B-S200502/Capstone_490_Software/hardware/3D_Design/component_step_files/pi_camera_g_detailed.step

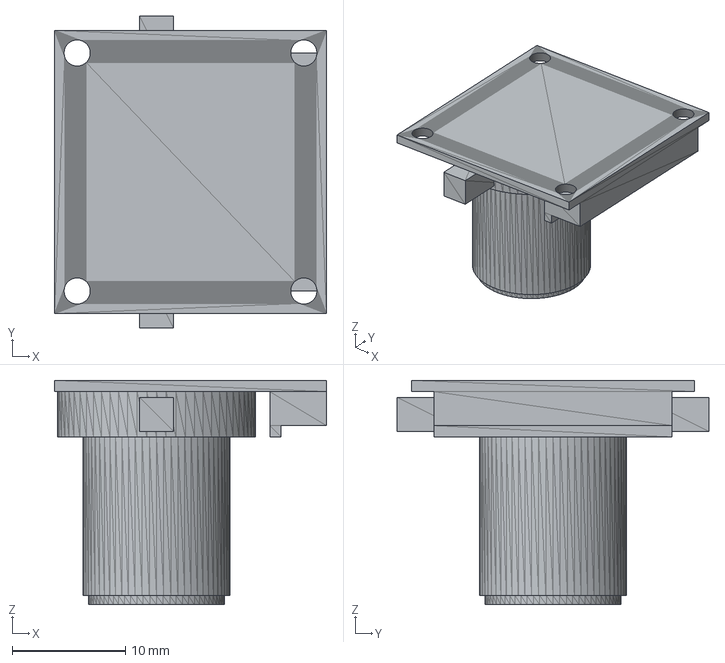
[picture p15: CAD file, 2026-03-08]
hardware/3D_Design/component_step_files/pi_camera_g_detailed.step
24.0 x 27.5 x 19.8 mm
