B-S200502/Capstone_490_Software/hardware/3D_Design/just_in_case_saves/V2_AC_test1.FCStd

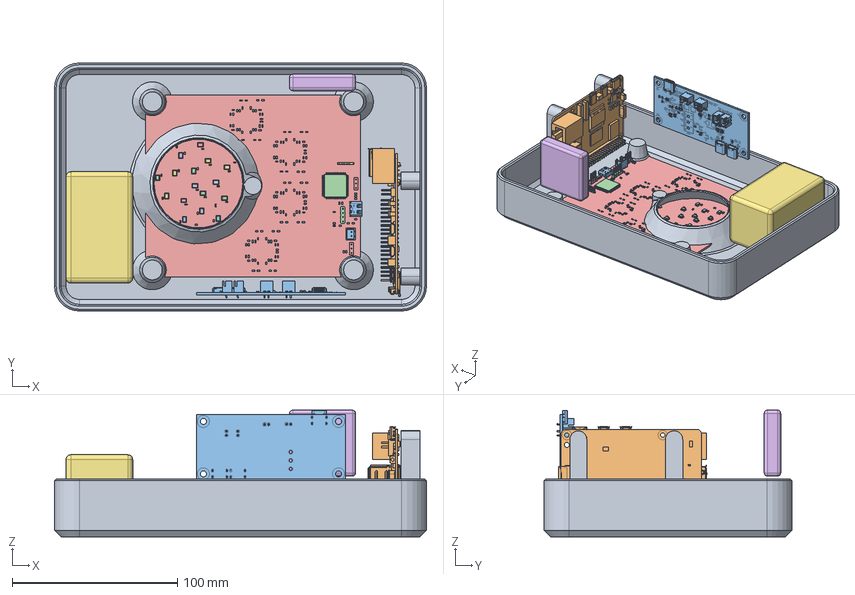
[picture p16: CAD file, 2026-03-08]
hardware/3D_Design/just_in_case_saves/V2_AC_test1.FCStd
225.0 x 150.0 x 76.7 mm
Back
Pi5
PowerBoard
R_0603_1608Metric
C_0603_1608Metric
R_0603_1608Metric001
MIC-SMD_6P_L3.5-W2.7_SPH1878LR5H-1
R_0603_1608Metric002
R_0603_1608Metric003
C_0603_1608Metric001
R_0603_1608Metric004
R_0603_1608Metric005
R_0603_1608Metric006
C_0603_1608Metric002
R_0603_1608Metric007
R_0603_1608Metric008
R_0603_1608Metric009
R_0603_1608Metric010
MIC-SMD_6P_L3.5-W2.7_SPH1878LR5H-002
R_0603_1608Metric011
PinHeader_1x03_P2.54mm_Vertical
R_0603_1608Metric012
R_0603_1608Metric013
R_0603_1608Metric014
R_0603_1608Metric015
R_0603_1608Metric016
R_0603_1608Metric017
MIC-SMD_6P_L3.5-W2.7_SPH1878LR5H-003
R_0603_1608Metric018
R_0603_1608Metric019
R_0603_1608Metric020
C_0603_1608Metric003
R_0603_1608Metric021
R_0603_1608Metric022
R_0603_1608Metric023
C_0603_1608Metric004
R_0603_1608Metric024
R_0603_1608Metric025
MIC-SMD_6P_L3.5-W2.7_SPH1878LR5H-004
R_0603_1608Metric026
R_0603_1608Metric027
C_0603_1608Metric005
R_0603_1608Metric028
R_0603_1608Metric029
R_0603_1608Metric030
R_0603_1608Metric031
R_0603_1608Metric032
R_0603_1608Metric033
C_0603_1608Metric006
R_0603_1608Metric034
C_0603_1608Metric007
R_0603_1608Metric035
R_0603_1608Metric036
R_0603_1608Metric037
R_0603_1608Metric038
R_0603_1608Metric039
R_0603_1608Metric040
R_0603_1608Metric041
R_0603_1608Metric042
R_0603_1608Metric043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
