B-S200502/Capstone_490_Software/hardware/3D_Design/result_step_files/BACK-AcousticImager-Fusion001.step

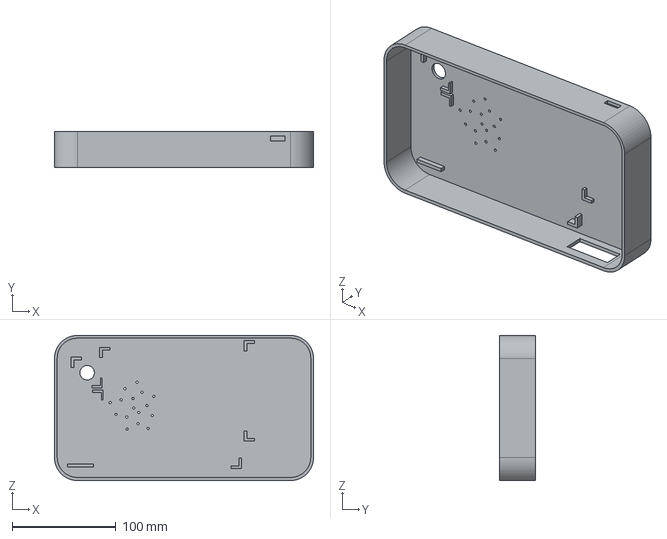
[picture p17: CAD file, 2026-02-12]
hardware/3D_Design/result_step_files/BACK-AcousticImager-Fusion001.step
250.0 x 35.0 x 140.0 mm
