B-S200502/Capstone_490_Software/src/hardware/result_step_files/bottom/BL_sink.step

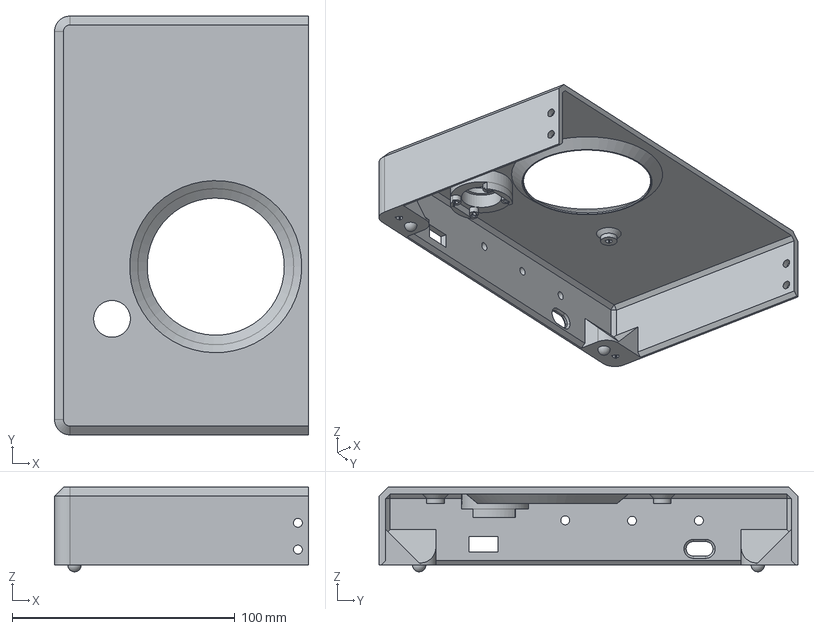
[picture p18: CAD file, 2026-05-04]
src/hardware/result_step_files/bottom/BL_sink.step
114.0 x 188.0 x 38.0 mm
