B-S200502/Capstone_490_Software/src/hardware/result_step_files/top/TL.step

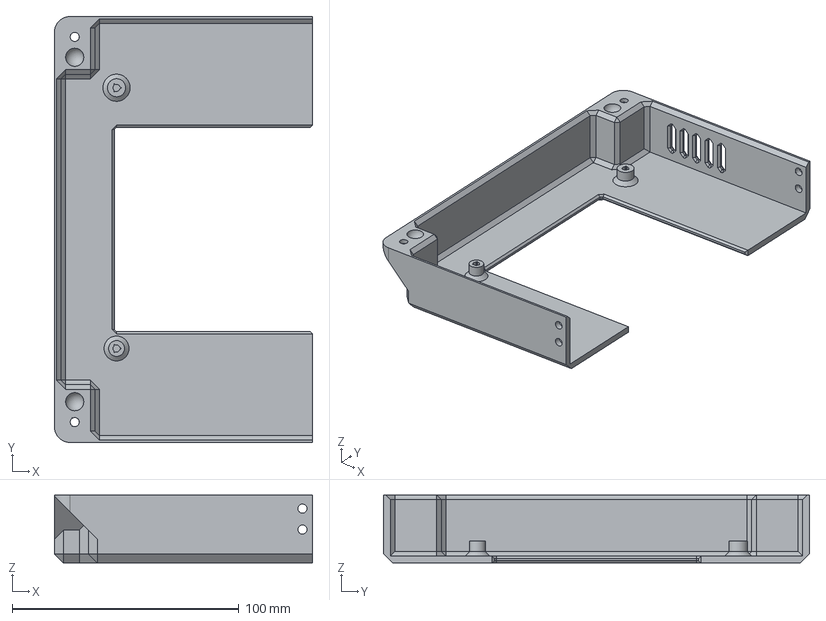
[picture p19: CAD file, 2026-05-04]
src/hardware/result_step_files/top/TL.step
114.0 x 188.0 x 30.0 mm
