B-S200502/Capstone_490_Software/hardware/3D_Design/component_step_files/low_level_components/SPH8878LR5H_1_Accurate.step

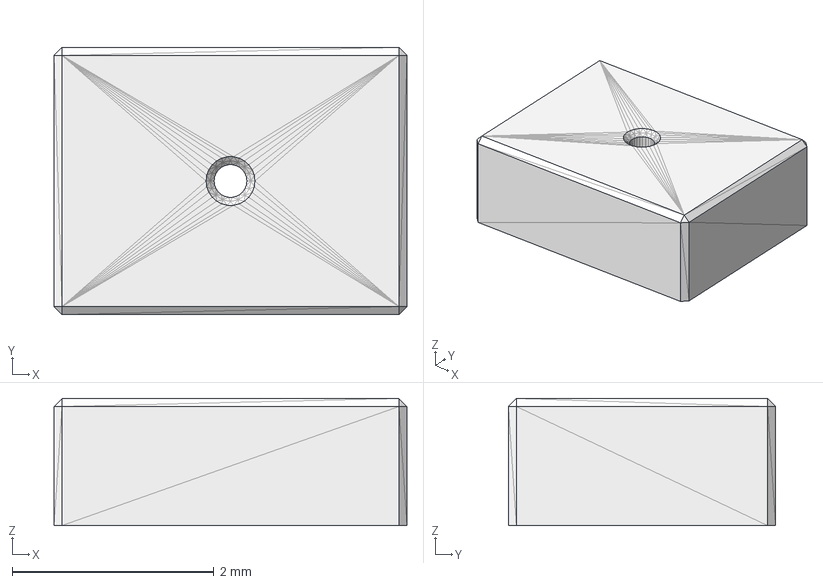
[picture p20: CAD file, 2026-02-10]
hardware/3D_Design/component_step_files/low_level_components/SPH8878LR5H_1_Accurate.step
3.50 x 2.65 x 1.26 mm
