B-S200502/Capstone_490_Software/hardware/3D_Design/component_step_files/Power Board.step

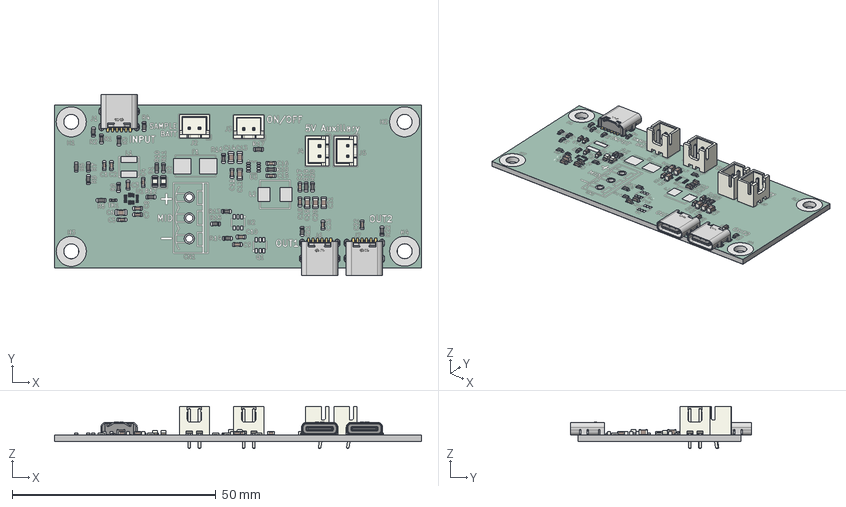
[picture p21: CAD file, 2026-02-10]
hardware/3D_Design/component_step_files/Power Board.step
90.0 x 44.4 x 10.4 mm
C_0805_2012Metric x 7
R_0603_1608Metric x 22
USB-C-SMD_TYPE-C-6P-WTL8.35-108 x 3
LED_0805_2012Metric x 2
JST_XH_B2B-XH-A_1x02_P2.50mm_Vertical x 4
C_0603_1608Metric x 16
R_0402_1005Metric
Power Board_copper
Power Board_pad
Power Board_via
Power Board_silkscreen
Power Board_soldermask x 2
Power Board_PCB
