B-S200502/Capstone_490_Software/hardware/3D_Design/just_in_case_saves/AcousticImager.FCStd

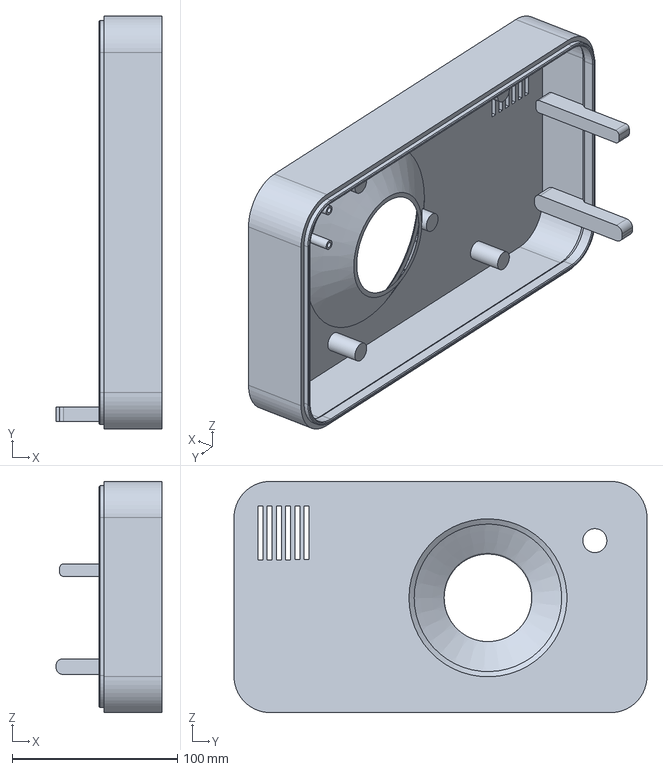
[picture p22: CAD file, 2026-03-08]
hardware/3D_Design/just_in_case_saves/AcousticImager.FCStd
64.0 x 250.0 x 140.0 mm
