B-S200502/Capstone_490_Software/hardware/3D_Design/component_step_files/lcd 7inch cap 1024 600.step

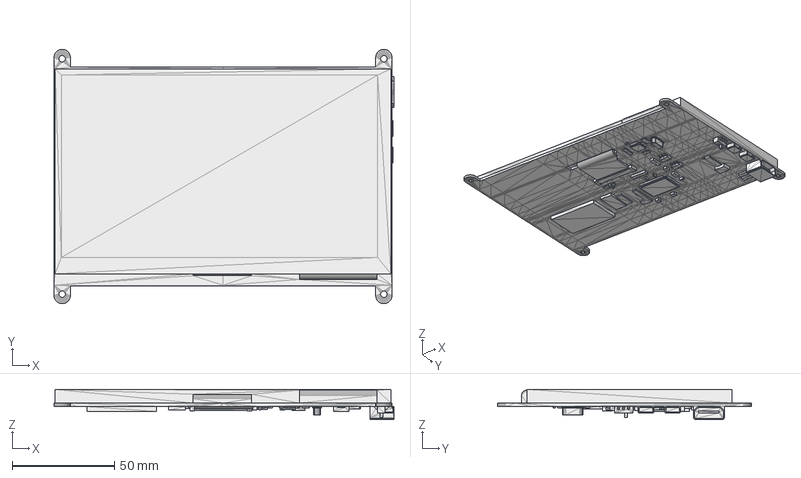
[picture p23: CAD file, 2026-02-10]
hardware/3D_Design/component_step_files/lcd 7inch cap 1024 600.step
166.0 x 124.3 x 14.8 mm
