B-S200502/Capstone_490_Software/hardware/3D_Design/component_step_files/low_level_components/QFP50P2200X2200X160-144N.step

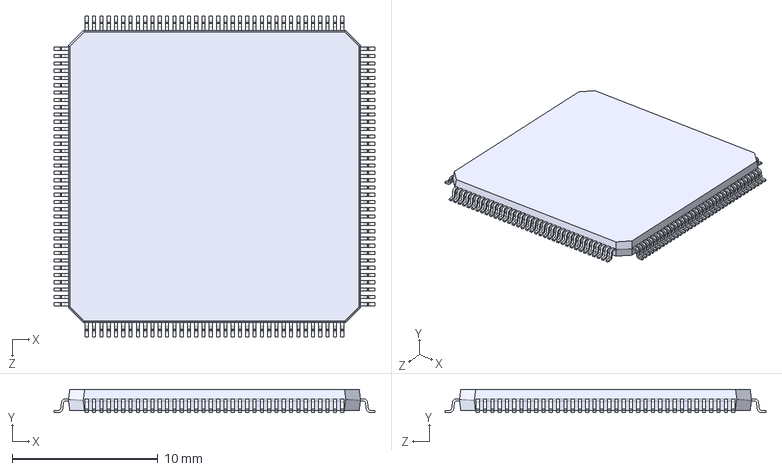
[picture p24: CAD file, 2026-02-10]
hardware/3D_Design/component_step_files/low_level_components/QFP50P2200X2200X160-144N.step
22.0 x 1.60 x 22.0 mm
