B-S200502/Capstone_490_Software/hardware/3D_Design/component_step_files/low_level_components/TPH2504-TR.stp

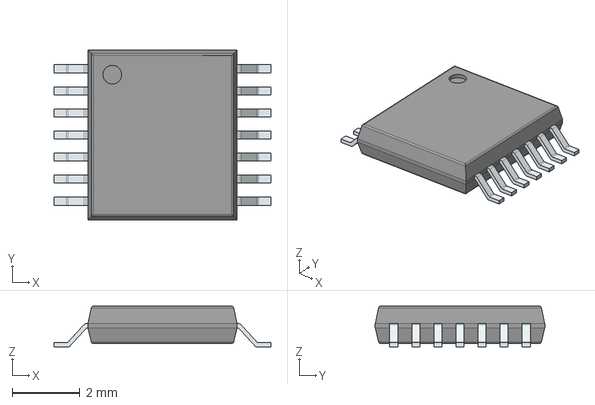
[picture p25: CAD file, 2026-02-10]
hardware/3D_Design/component_step_files/low_level_components/TPH2504-TR.stp
6.40 x 5.00 x 1.20 mm
PinsArrayLR
