B-S200502/Capstone_490_Software/hardware/3D_Design/component_step_files/RaspberryPi5.step

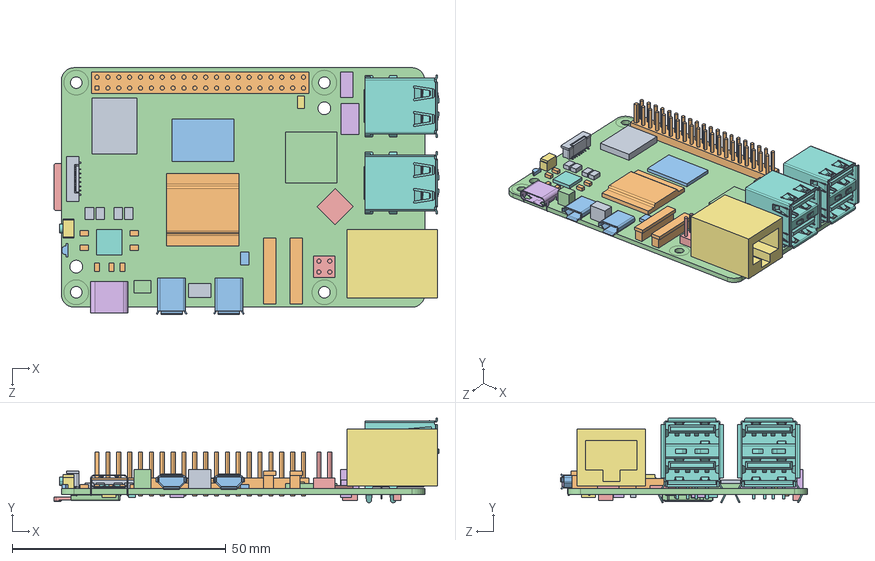
[picture p26: CAD file, 2026-02-10]
hardware/3D_Design/component_step_files/RaspberryPi5.step
90.0 x 19.8 x 57.7 mm
PCB_for REF 060923
GPIO Header for REF
Micro HDMI for REF x 2
SD CARD for REF
USB-C for REF
RJ45 for REF
USB for REF x 2
PCIe for REF
CAM-DISP for REF x 2
LED for REF
BAT Header for REF
PoE Header for REF
FAN Header for REF
SWITCH for REF
UART for REF
