B-S200502/Capstone_490_Software/hardware/3D_Design/component_step_files/LQFP100-14x14mm.step

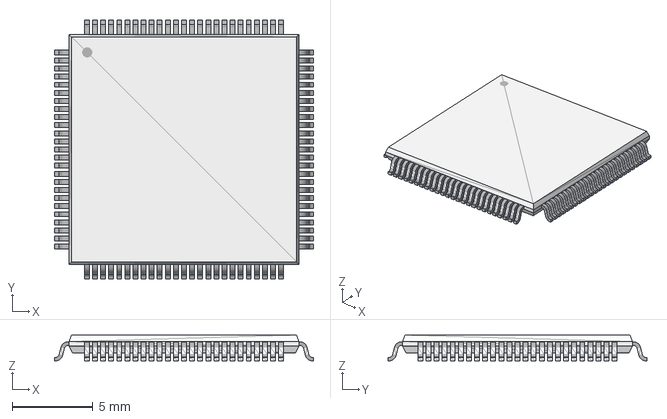
[picture p27: CAD file, 2026-02-10]
hardware/3D_Design/component_step_files/LQFP100-14x14mm.step
16.0 x 16.0 x 1.60 mm
