B-S200502/Capstone_490_Software/utilities/calibration/calibration_suite_cal_dump.txt

=== Calibration Suite (stop acoustic imager for SPI steps) ===
STEP_PROGRESS 0 7
[0] Silence check (env quiet enough for gain cal)...
SILENCE_START 1.5
  max_total_power=8.682e+01 threshold=1.000e+09 frames=26 -> PASS
  FrameReadyGPIO init failed (No GPIO backend available. Install gpiozero or run on a Raspberry Pi with RPi.GPIO.); continuing without GPIO wait
  parse_full_frame: magic 0xCD3DDAE2 != expected 0xAABBCCDD, buf[:8]=e2da3dcd5b393edb
  parse_full_frame: magic 0x7B7B7B7B != expected 0xAABBCCDD, buf[:8]=7b7b7b7b7b7b7b7b
  parse_full_frame: magic 0xE4D5E3BD != expected 0xAABBCCDD, buf[:8]=bde3d5e4bc37b533
  parse_full_frame: magic 0xC603B90E != expected 0xAABBCCDD, buf[:8]=0eb903c6c3bb586f
  parse_full_frame: magic 0xC7C7C7C7 != expected 0xAABBCCDD, buf[:8]=c7c7c7c7c7c7c7c7
  parse_full_frame: magic 0xF63A11B6 != expected 0xAABBCCDD, buf[:8]=b6113af627d4b976
  parse_full_frame: magic 0x00000000 != expected 0xAABBCCDD, buf[:8]=0000000000000000
  parse_full_frame: magic 0x5C3CAA6A != expected 0xAABBCCDD, buf[:8]=6aaa3c5c7bf83b3c
  OK
STEP_PROGRESS 1 7
[1] Pin monitor (ribbon cable, 5 runs)...
  Pin monitor (SPI0, 5 runs)
  Physical   BCM    Usage                      Value
  ----------------------------------------------------------
  22         25     Gain Ctrl                  0
  26         7      MCU status                 1
  27         0      RPi status                 0
  20         -      GND                        -
  23         11     SCK                        0
  24         8      NSS (SPI0 CE0)             1
  21         9      MISO                       0
  19         10     MOSI                       0
  25         -      GND                        -
  28         1      NRST                       1
  SPI: /dev/spidev0.0  exists=yes  in_use=no

  22         25     Gain Ctrl                  0
  26         7      MCU status                 1
  27         0      RPi status                 0
  20         -      GND                        -
  23         11     SCK                        0
  24         8      NSS (SPI0 CE0)             1
  21         9      MISO                       0
  19         10     MOSI                       0
  25         -      GND                        -
  28         1      NRST                       1
  SPI: /dev/spidev0.0  exists=yes  in_use=no

  22         25     Gain Ctrl                  0
  26         7      MCU status                 1
  27         0      RPi status                 0
  20         -      GND                        -
  23         11     SCK                        0
  24         8      NSS (SPI0 CE0)             1
  21         9      MISO                       0
  19         10     MOSI                       0
  25         -      GND                        -
  28         1      NRST                       1
  SPI: /dev/spidev0.0  exists=yes  in_use=no

  22         25     Gain Ctrl                  0
  26         7      MCU status                 1
  27         0      RPi status                 0
  20         -      GND                        -
  23         11     SCK                        0
  24         8      NSS (SPI0 CE0)             1
  21         9      MISO                       0
  19         10     MOSI                       0
  25         -      GND                        -
  28         1      NRST                       1
  SPI: /dev/spidev0.0  exists=yes  in_use=no

  22         25     Gain Ctrl                  0
  26         7      MCU status                 1
  27         0      RPi status                 0
  20         -      GND                        -
  23         11     SCK                        0
  24         8      NSS (SPI0 CE0)             1
  21         9      MISO                       0
  19         10     MOSI                       0
  25         -      GND                        -
  28         1      NRST                       1
  SPI: /dev/spidev0.0  exists=yes  in_use=no
  OK
STEP_PROGRESS 2 7
[2] Array geometry & config alignment...
  Calibration test setup (see utilities/calibration/calibration_test.md):
    distance_inches = 5.0
    offset_inches   = 7.0 (+ = array right of camera center)
    note            = Camera left, board right, same heading

  Config (config.py):
    CALIBRATION_DISTANCE_INCHES = 5.0
    CALIBRATION_OFFSET_INCHES   = 7.0
    CALIBRATION_NOTE             = 'Camera left, board right, same heading'
    HW geometry: x_coords_hw, y_coords_hw (source: config.py), length 16

  Validate OK: config matches calibration_test.md
  Geometry OK (config.py matches array_geometry)
STEP_PROGRESS 3 7
[3] SPI devices...
  === Boot config (SPI enabled?) ===
  --- /boot/config.txt ---
  --- /boot/firmware/config.txt ---
  6:dtparam=i2c_arm=on
  7:#dtparam=i2s=on
  8:dtparam=spi=on
  9:dtoverlay=spi1-3cs
  12:dtparam=audio=on
  53:dtparam=uart0=on

  === SPI device nodes ===
  crw-rw---- 1 root spi 153, 0 Mar 29 20:03 /dev/spidev0.0
  crw-rw---- 1 root spi 153, 1 Mar 29 20:03 /dev/spidev0.1
  crw-rw---- 1 root spi 153, 4 Mar 29 20:03 /dev/spidev1.0
  crw-rw---- 1 root spi 153, 5 Mar 29 20:03 /dev/spidev10.0
  crw-rw---- 1 root spi 153, 3 Mar 29 20:03 /dev/spidev1.1
  crw-rw---- 1 root spi 153, 2 Mar 29 20:03 /dev/spidev1.2

  === Kernel SPI modules ===
  spidev                 49152  0
  spi_bcm2835            49152  0
  spi_dw_mmio            49152  0
  spi_dw                 49152  1 spi_dw_mmio

  === dmesg (SPI) ===
STEP_PROGRESS 4 7
[4] Parsing (magic probe) & frame rate...
  Probing /dev/spidev1.2, frame_size=32801, sync=False
  Magic LE: dd cc bb aa  |  BE: aa bb cc dd  |  bit_rev LE: bb33dd55
  ------------------------------------------------------------
  mode=0 lsbfirst=False: magic@[0x0] BE no bit_rev no
  mode=0 lsbfirst=True: lsbfirst not supported
  mode=1 lsbfirst=False: magic@[0x7609] BE no bit_rev no
  mode=1 lsbfirst=True: lsbfirst not supported
  mode=2 lsbfirst=False: magic no BE no bit_rev no
  mode=2 lsbfirst=True: lsbfirst not supported
  mode=3 lsbfirst=False: magic no BE no bit_rev no
  mode=3 lsbfirst=True: lsbfirst not supported
  ------------------------------------------------------------
  At least one setting saw magic (LE/BE/bit_rev). Consider aligning config to that.
  SPI_MAX_SPEED_HZ = 30000000
  FPS = 33.7  frames_ok = 51  bad_parse = 10  bad_crc = 0
  OK
STEP_PROGRESS 5 7
[5] Metrics (gain normalization)...
  --- Per-mic levels (LOW gain, averaged over 5 frames) ---
    Total power (sum of squared L2 per mic): 1.514302e+01
    Max mic L2: 2.921956e+00  Min mic L2: 1.000000e-12
    Ratio max/min: >1e6

    mic   ADC   L2 norm      dB vs max   ratio    suggested gain (to match max)
    ---   ---   ---------   ---------   -----    -----------------------------
      0   ADC1   2.237973e-01   -11.2 dB    0.077     13.06
      1   ADC1   1.036806e-06   -64.5 dB    0.000     100+
      2   ADC1   1.000000e-12   -124.7 dB    0.000     100+
      3   ADC1   3.785485e-01   -8.9 dB    0.130     7.72
      4   ADC2   9.556695e-01   -4.9 dB    0.327     3.06
      5   ADC2   2.921956e+00   +0.0 dB    1.000     1.00
      6   ADC2   2.534621e-01   -10.6 dB    0.087     11.53
      7   ADC2   3.062969e-01   -9.8 dB    0.105     9.54
      8   ADC3   3.859578e-01   -8.8 dB    0.132     7.57
      9   ADC3   1.459258e+00   -3.0 dB    0.499     2.00
     10   ADC3   2.499033e-01   -10.7 dB    0.086     11.69
     11   ADC3   3.575276e-01   -9.1 dB    0.122     8.17
     12   ADC4   3.965507e-01   -8.7 dB    0.136     7.37
     13   ADC4   1.544285e+00   -2.8 dB    0.529     1.89
     14   ADC4   3.028370e-01   -9.8 dB    0.104     9.65
     15   ADC4   4.878385e-01   -7.8 dB    0.167     5.99

    ADC1 (mics [0, 1, 2, 3]): mean dB vs max = -52.3 dB
    ADC2 (mics [4, 5, 6, 7]): mean dB vs max = -6.3 dB
    ADC3 (mics [8, 9, 10, 11]): mean dB vs max = -7.9 dB
    ADC4 (mics [12, 13, 14, 15]): mean dB vs max = -7.3 dB

    Mics with level < 35% of max (candidates for SPI_MIC_GAIN boost): [0, 1, 2, 3, 4, 6, 7,
    Example: set those indices to suggested gain in config.SPI_MIC_GAIN.

  --- Per-mic levels (HIGH gain, averaged over 5 frames) ---
    Total power (sum of squared L2 per mic): 1.073882e+01
    Max mic L2: 2.336752e+00  Min mic L2: 1.000000e-12
    Ratio max/min: >1e6

    mic   ADC   L2 norm      dB vs max   ratio    suggested gain (to match max)
    ---   ---   ---------   ---------   -----    -----------------------------
      0   ADC1   1.972839e-01   -10.7 dB    0.084     11.84
      1   ADC1   1.750141e-12   -121.3 dB    0.000     100+
      2   ADC1   1.000000e-12   -123.7 dB    0.000     100+
      3   ADC1   3.881832e-01   -7.8 dB    0.166     6.02
      4   ADC2   7.636846e-01   -4.9 dB    0.327     3.06
      5   ADC2   2.336752e+00   +0.0 dB    1.000     1.00
      6   ADC2   3.368773e-01   -8.4 dB    0.144     6.94
      7   ADC2   2.829051e-01   -9.2 dB    0.121     8.26
      8   ADC3   3.695423e-01   -8.0 dB    0.158     6.32
      9   ADC3   1.425029e+00   -2.1 dB    0.610     1.64
     10   ADC3   2.577006e-01   -9.6 dB    0.110     9.07
     11   ADC3   3.189684e-01   -8.6 dB    0.137     7.33
     12   ADC4   3.695968e-01   -8.0 dB    0.158     6.32
     13   ADC4   1.282458e+00   -2.6 dB    0.549     1.82
     14   ADC4   2.724119e-01   -9.3 dB    0.117     8.58
     15   ADC4   3.480517e-01   -8.3 dB    0.149     6.71

    ADC1 (mics [0, 1, 2, 3]): mean dB vs max = -65.9 dB
    ADC2 (mics [4, 5, 6, 7]): mean dB vs max = -5.6 dB
    ADC3 (mics [8, 9, 10, 11]): mean dB vs max = -7.1 dB
    ADC4 (mics [12, 13, 14, 15]): mean dB vs max = -7.1 dB

    Mics with level < 35% of max (candidates for SPI_MIC_GAIN boost): [0, 1, 2, 3, 4, 6, 7,
    Example: set those indices to suggested gain in config.SPI_MIC_GAIN.

    Wrote SPI_MIC_GAIN to /home/acousticlord/Capstone_490_Software/src/software/acoustic_ima
    Restart the acoustic imager for changes to take effect.
  FrameReadyGPIO init failed (No GPIO backend available. Install gpiozero or run on a Raspbe
  /home/acousticlord/Capstone_490_Software/utilities/calibration/metrics_debug.py:84: Runtim
    scale = np.where(mag > _FFT_MAG_CAP, _FFT_MAG_CAP / (mag + 1e-30), 1.0)
  OK
STEP_PROGRESS 6 7
[6] Post-gain sanity (ratio check)...
  --- Per-mic levels (LOW gain, latest of 3 frames) ---
    Total power (sum of squared L2 per mic): 5.343658e+01
    Max mic L2: 6.280973e+00  Min mic L2: 1.000000e-12
    Ratio max/min: >1e6

    mic   ADC   L2 norm      dB vs max   ratio    suggested gain (to match max)
    ---   ---   ---------   ---------   -----    -----------------------------
      0   ADC1   4.574178e-01   -11.4 dB    0.073     13.73
      1   ADC1   1.000000e-12   -128.0 dB    0.000     100+
      2   ADC1   1.000000e-12   -128.0 dB    0.000     100+
      3   ADC1   6.849095e-01   -9.6 dB    0.109     9.17
      4   ADC2   1.230671e+00   -7.1 dB    0.196     5.10
      5   ADC2   6.280973e+00   +0.0 dB    1.000     1.00
      6   ADC2   5.488811e-01   -10.6 dB    0.087     11.44
      7   ADC2   6.230463e-01   -10.0 dB    0.099     10.08
      8   ADC3   5.640818e-01   -10.5 dB    0.090     11.13
      9   ADC3   2.859566e+00   -3.4 dB    0.455     2.20
     10   ADC3   5.691763e-01   -10.4 dB    0.091     11.04
     11   ADC3   7.282270e-01   -9.4 dB    0.116     8.63
     12   ADC4   8.197829e-01   -8.8 dB    0.131     7.66
     13   ADC4   2.141336e-02   -24.7 dB    0.003     100+
     14   ADC4   6.287157e-01   -10.0 dB    0.100     9.99
     15   ADC4   8.283961e-01   -8.8 dB    0.132     7.58

    ADC1 (mics [0, 1, 2, 3]): mean dB vs max = -69.2 dB
    ADC2 (mics [4, 5, 6, 7]): mean dB vs max = -6.9 dB
    ADC3 (mics [8, 9, 10, 11]): mean dB vs max = -8.4 dB
    ADC4 (mics [12, 13, 14, 15]): mean dB vs max = -13.1 dB

    Mics with level < 35% of max (candidates for SPI_MIC_GAIN boost): [0, 1, 2, 3, 4, 6, 7,
    Example: set those indices to suggested gain in config.SPI_MIC_GAIN.

  --- Per-mic levels (HIGH gain, latest of 3 frames) ---
    Total power (sum of squared L2 per mic): 5.501996e+01
    Max mic L2: 4.724180e+00  Min mic L2: 1.000000e-12
    Ratio max/min: >1e6

    mic   ADC   L2 norm      dB vs max   ratio    suggested gain (to match max)
    ---   ---   ---------   ---------   -----    -----------------------------
      0   ADC1   9.413223e-01   -7.0 dB    0.199     5.02
      1   ADC1   1.000000e-12   -126.7 dB    0.000     100+
      2   ADC1   1.000000e-12   -126.7 dB    0.000     100+
      3   ADC1   7.956678e-01   -7.7 dB    0.168     5.94
      4   ADC2   2.945812e+00   -2.1 dB    0.624     1.60
      5   ADC2   4.133307e+00   -0.6 dB    0.875     1.14
      6   ADC2   6.526183e-01   -8.6 dB    0.138     7.24
      7   ADC2   6.358511e-01   -8.7 dB    0.135     7.43
      8   ADC3   4.804072e-01   -9.9 dB    0.102     9.83
      9   ADC3   4.724180e+00   +0.0 dB    1.000     1.00
     10   ADC3   6.563294e-01   -8.6 dB    0.139     7.20
     11   ADC3   8.971436e-01   -7.2 dB    0.190     5.27
     12   ADC4   9.981400e-01   -6.8 dB    0.211     4.73
     13   ADC4   5.678493e-01   -9.2 dB    0.120     8.32
     14   ADC4   8.077054e-01   -7.7 dB    0.171     5.85
     15   ADC4   1.073825e+00   -6.4 dB    0.227     4.40

    ADC1 (mics [0, 1, 2, 3]): mean dB vs max = -67.1 dB
    ADC2 (mics [4, 5, 6, 7]): mean dB vs max = -5.0 dB
    ADC3 (mics [8, 9, 10, 11]): mean dB vs max = -6.4 dB
    ADC4 (mics [12, 13, 14, 15]): mean dB vs max = -7.5 dB

    Mics with level < 35% of max (candidates for SPI_MIC_GAIN boost): [0, 1, 2, 3, 6, 7, 8,
    Example: set those indices to suggested gain in config.SPI_MIC_GAIN.
  FrameReadyGPIO init failed (No GPIO backend available. Install gpiozero or run on a Raspbe
  /home/acousticlord/Capstone_490_Software/utilities/calibration/metrics_debug.py:84: Runtim
    scale = np.where(mag > _FFT_MAG_CAP, _FFT_MAG_CAP / (mag + 1e-30), 1.0)
  OK (ratio in output)
CPU temp: 67.8 C
=== Done: 7/7 steps passed ===
[stderr] FrameReadyGPIO init failed (No GPIO backend available. Install gpiozero or run on a Raspberry Pi with RPi.GPIO.); continuing without GPIO wait
[stderr] parse_full_frame: magic 0x77330F0F != expected 0xAABBCCDD, buf[:8]=0f0f33775d176978
[stderr] parse_full_frame: magic 0x3A3A3A3A != expected 0xAABBCCDD, buf[:8]=3a3a3a3a3a3a3a3a
[stderr] parse_full_frame: magic 0x3B569375 != expected 0xAABBCCDD, buf[:8]=7593563bb19d3f3d
[stderr] parse_full_frame: magic 0xA4A4A4A4 != expected 0xAABBCCDD, buf[:8]=a4a4a4a4a4a4a4a4
[stderr] parse_full_frame: magic 0x61EA3ADB != expected 0xAABBCCDD, buf[:8]=db3aea616d3b18d4
[stderr] parse_full_frame: magic 0x27A90C65 != expected 0xAABBCCDD, buf[:8]=650ca9271914a8a6
[stderr] parse_full_frame: magic 0x59595959 != expected 0xAABBCCDD, buf[:8]=5959595959595959
[stderr] parse_full_frame: magic 0x97563D0A != expected 0xAABBCCDD, buf[:8]=0a3d5697c43a61e1
[stderr] parse_full_frame: magic 0x0D0D0D0D != expected 0xAABBCCDD, buf[:8]=0d0d0d0d0d0d0d0d
[stderr] parse_full_frame: magic 0x21CF453D != expected 0xAABBCCDD, buf[:8]=3d45cf21bdaba9aa
